Nicowars/poncho-bluetooth/Poncho/modelos/Poncho_Chico/meta/ponchoB.png

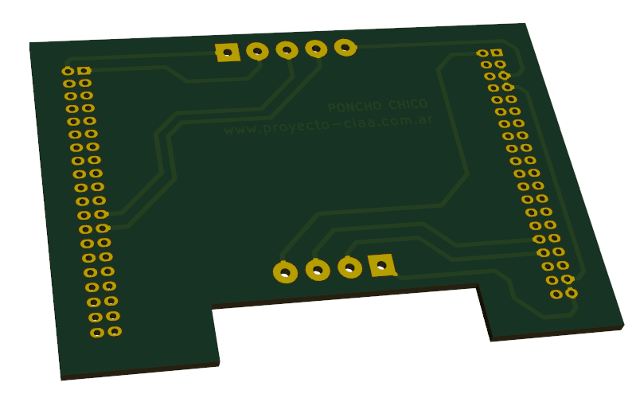
Poncho/modelos/Poncho_Chico/meta/ponchoB.png
