Nicowars/poncho-bluetooth/Poncho/modelos/Poncho_Chico/meta/ponchoF.png

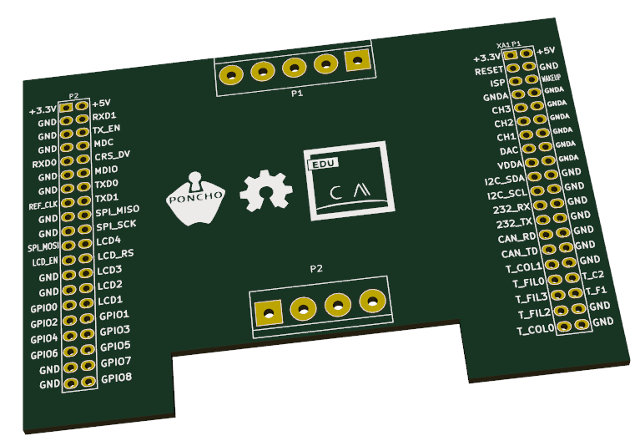
Poncho/modelos/Poncho_Chico/meta/ponchoF.png
