Nicowars/poncho-bluetooth/Poncho/modelos/Poncho_Derecho/meta/ponchoFb.png

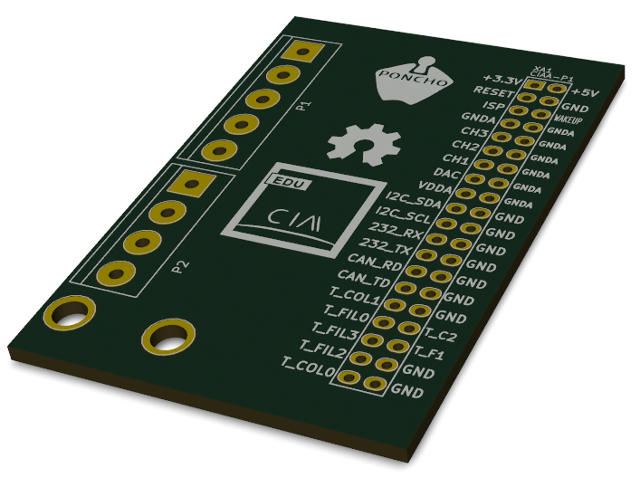
Poncho/modelos/Poncho_Derecho/meta/ponchoFb.png
