Nicowars/poncho-bluetooth/Poncho/modelos/Poncho_Grande/meta/poncho_grande.png

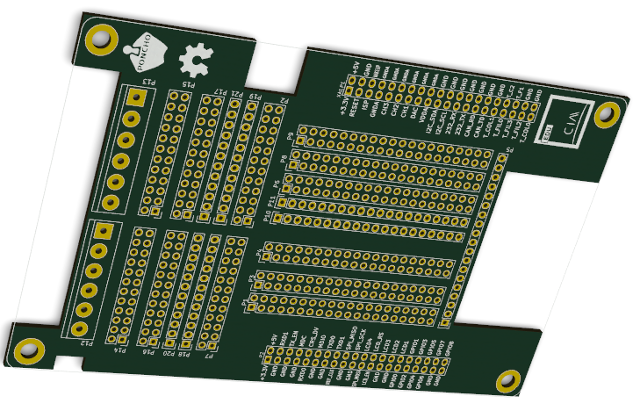
Poncho/modelos/Poncho_Grande/meta/poncho_grande.png
