Nicowars/poncho-bluetooth/Poncho/modelos/Poncho_Izquierdo/meta/ponchoF.png

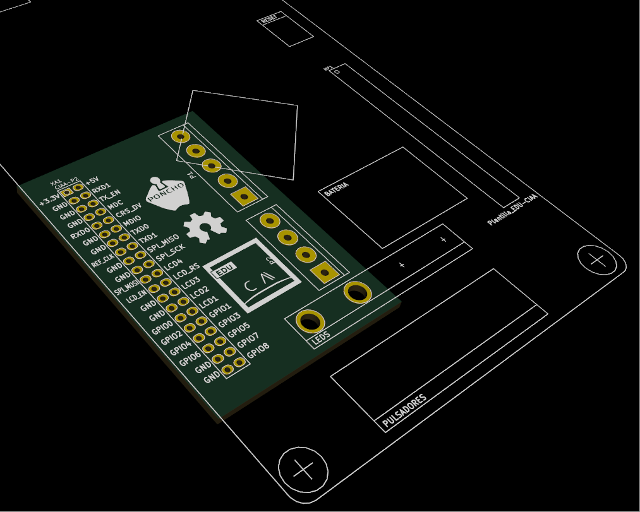
Poncho/modelos/Poncho_Izquierdo/meta/ponchoF.png
