Nicowars/poncho-bluetooth/Poncho/modelos/Poncho_Izquierdo/meta/ponchoFb.png

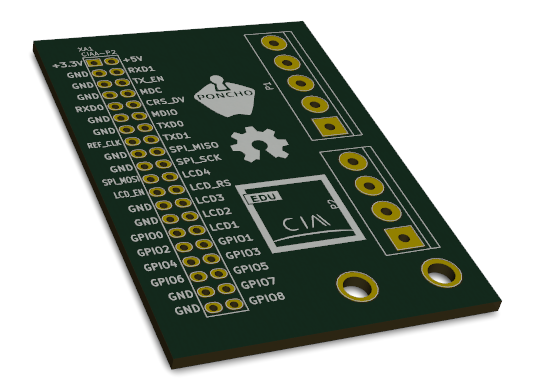
Poncho/modelos/Poncho_Izquierdo/meta/ponchoFb.png
