Nicowars/poncho-bluetooth/Poncho/modelos/Poncho_Mediano/meta/ponchoF.png

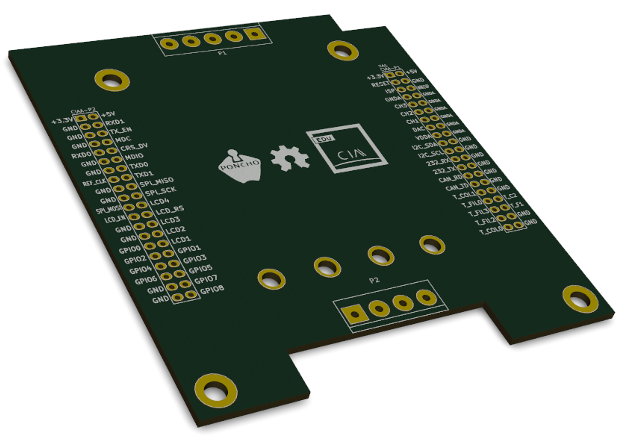
Poncho/modelos/Poncho_Mediano/meta/ponchoF.png
