Nicowars/poncho-bluetooth/projects/bluetooth-rn4020/inc/bluetooth-rn4020.h

/* 
 * Autores
 * ---------------------------
 * Gabriel Morgillo
 * Nicolás Laurella
 * Alex Muriel
 * Jaime Zubieta Battista
 * Manuel Solito
 */

#ifndef BLUETOOTH-RN4020_H_
#define BLUETOOTH-RN4020_H_

/*==================[end of file]============================================*/
#endif 
